LEDs-by-glowingkitty/GlowSign/Cover PCB Circle Edition/pure_pcb_front.jpg

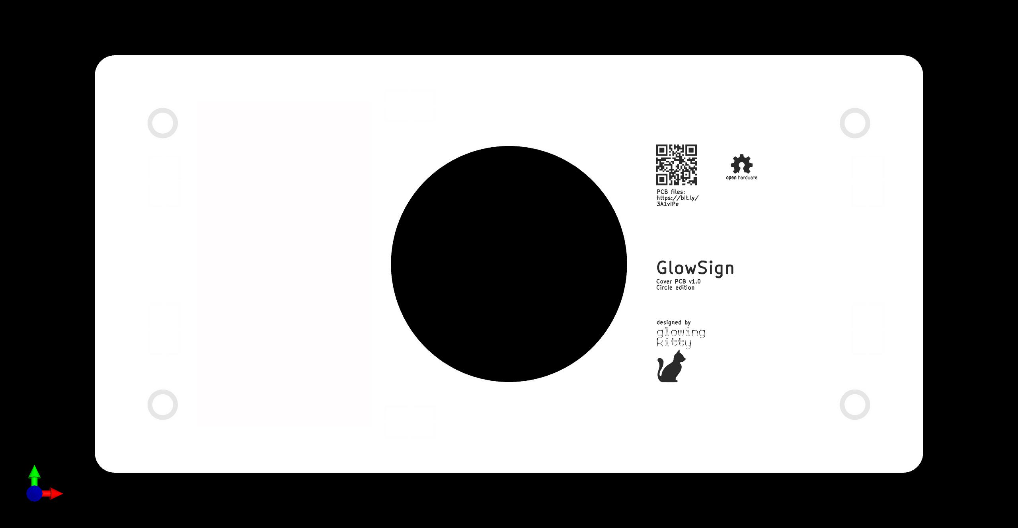
Cover PCB Circle Edition/pure_pcb_front.jpg
