LEDs-by-glowingkitty/GlowSign/GlowSign Battery Sticker Back @300dpi (Page 1).png

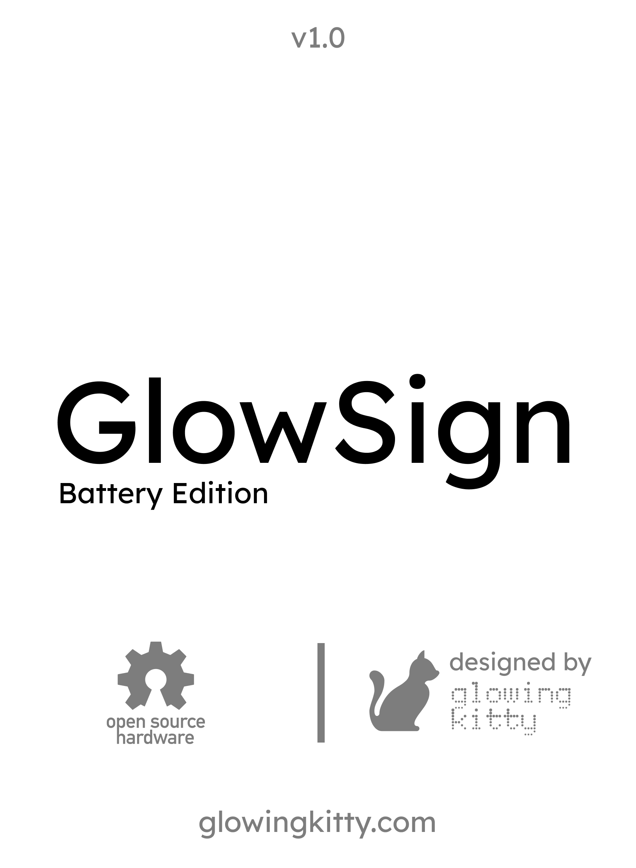
GlowSign Battery Sticker Back @300dpi (Page 1).png
