LEDs-by-glowingkitty/GlowSign/Main PCB/pure_pcb_front.jpg

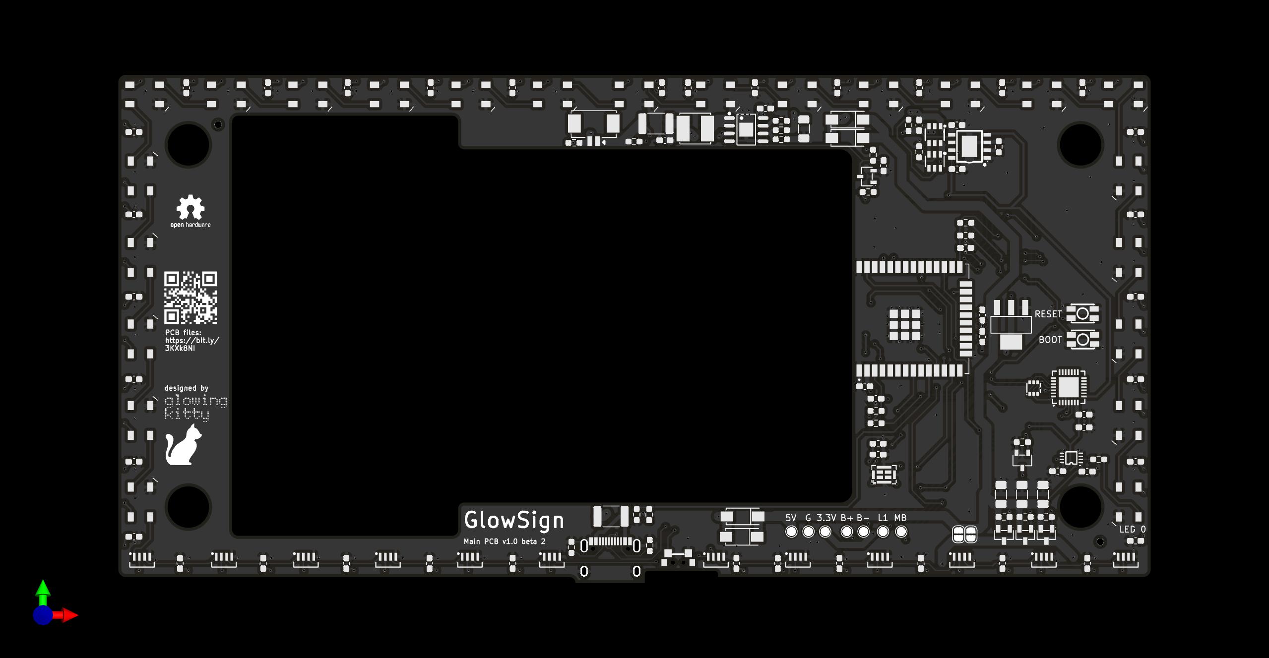
Main PCB/pure_pcb_front.jpg
